ggrummer/Dazzelite/Dazz12/instr_dpram_sect2/testbench/dut_params.v

localparam FAMILY = "iCE40UP";
localparam MEM_ID = "instr_dpram_sect2";
localparam MEM_SIZE = "32,256";
localparam WADDR_DEPTH = 256;
localparam WDATA_WIDTH = 32;
localparam RADDR_DEPTH = 256;
localparam RDATA_WIDTH = 32;
localparam WADDR_WIDTH = 8;
localparam REGMODE = "noreg";
localparam RADDR_WIDTH = 8;
localparam OUTPUT_CLK_EN = 0;
localparam RESETMODE = "sync";
localparam BYTE_ENABLE = 0;
localparam BYTE_WIDTH = 1;
localparam BYTE_SIZE = 8;
localparam ECC_ENABLE = 0;
localparam INIT_MODE = "mem_file";
localparam INIT_FILE = "misc/shootenballs_instr_dpram_sect2_copy.mem";
localparam INIT_FILE_FORMAT = "hex";
localparam INIT_VALUE_00 = "0x50608110107050004000417010704050404040304020401040008010500000000x00004000000000008000800F00008F0FAF0088E080C080AF800F100020000000";
localparam INIT_VALUE_01 = "0x10705000403040205060811010705000402040105060811010705000401040000x00000000800088E00000400000000000800080C00000400000000000800080AF";
localparam INIT_VALUE_02 = "0x000020008FF281101070500040504040506081101070500040404030506081100x00000000500040000000000080008F0F00004000000000008000AF0000004000";
localparam INIT_VALUE_03 = "0x00000000000000000000000000000000000000000000000000000000000000000x0000000000000000000000000000000000000000000000000000000000000000";
localparam INIT_VALUE_04 = "0x00000000000000000000000000000000000000000000000000000000000000000x0000000000000000000000000000000000000000000000000000000000000000";
localparam INIT_VALUE_05 = "0x00000000000000000000000000000000000000000000000000000000000000000x0000000000000000000000000000000000000000000000000000000000000000";
localparam INIT_VALUE_06 = "0x00000000000000000000000000000000000000000000000000000000000000000x0000000000000000000000000000000000000000000000000000000000000000";
localparam INIT_VALUE_07 = "0x00000000000000000000000000000000000000000000000000000000000000000x0000000000000000000000000000000000000000000000000000000000000000";
localparam INIT_VALUE_08 = "0x00000000000000000000000000000000000000000000000000000000000000000x0000000000000000000000000000000000000000000000000000000000000000";
localparam INIT_VALUE_09 = "0x00000000000000000000000000000000000000000000000000000000000000000x0000000000000000000000000000000000000000000000000000000000000000";
localparam INIT_VALUE_0A = "0x00000000000000000000000000000000000000000000000000000000000000000x0000000000000000000000000000000000000000000000000000000000000000";
localparam INIT_VALUE_0B = "0x00000000000000000000000000000000000000000000000000000000000000000x0000000000000000000000000000000000000000000000000000000000000000";
localparam INIT_VALUE_0C = "0x00000000000000000000000000000000000000000000000000000000000000000x0000000000000000000000000000000000000000000000000000000000000000";
localparam INIT_VALUE_0D = "0x00000000000000000000000000000000000000000000000000000000000000000x0000000000000000000000000000000000000000000000000000000000000000";
localparam INIT_VALUE_0E = "0x00000000000000000000000000000000000000000000000000000000000000000x0000000000000000000000000000000000000000000000000000000000000000";
localparam INIT_VALUE_0F = "0x00000000000000000000000000000000000000000000000000000000000000000x0000000000000000000000000000000000000000000000000000000000000000";
localparam INIT_VALUE_10 = "0x0000000000000000000000000000000000000000000000000000000000000000";
localparam INIT_VALUE_11 = "0x0000000000000000000000000000000000000000000000000000000000000000";
localparam INIT_VALUE_12 = "0x0000000000000000000000000000000000000000000000000000000000000000";
localparam INIT_VALUE_13 = "0x0000000000000000000000000000000000000000000000000000000000000000";
localparam INIT_VALUE_14 = "0x0000000000000000000000000000000000000000000000000000000000000000";
localparam INIT_VALUE_15 = "0x0000000000000000000000000000000000000000000000000000000000000000";
localparam INIT_VALUE_16 = "0x0000000000000000000000000000000000000000000000000000000000000000";
localparam INIT_VALUE_17 = "0x0000000000000000000000000000000000000000000000000000000000000000";
localparam INIT_VALUE_18 = "0x0000000000000000000000000000000000000000000000000000000000000000";
localparam INIT_VALUE_19 = "0x0000000000000000000000000000000000000000000000000000000000000000";
localparam INIT_VALUE_1A = "0x0000000000000000000000000000000000000000000000000000000000000000";
localparam INIT_VALUE_1B = "0x0000000000000000000000000000000000000000000000000000000000000000";
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
localparam INIT_VALUE_3E = "0x0000000000000000000000000000000000000000000000000000000000000000";
localparam INIT_VALUE_3F = "0x0000000000000000000000000000000000000000000000000000000000000000";
`define ICE40UP
