ggrummer/Dazzelite/Dazz12/instr_dpram_sect0/misc/instr_dpram_sect0_tmpl.v

    instr_dpram_sect0 __(.wr_clk_i( ),
        .rd_clk_i( ),
        .rst_i( ),
        .wr_clk_en_i( ),
        .rd_en_i( ),
        .rd_clk_en_i( ),
        .wr_en_i( ),
        .wr_data_i( ),
        .wr_addr_i( ),
        .rd_addr_i( ),
        .rd_data_o( ));
